hephaestushex/HexMote/assets/Case_(Assembly)_2026-Jul-08_06-05-27PM-000_CustomizedView10271644335_zip/frame.2.png

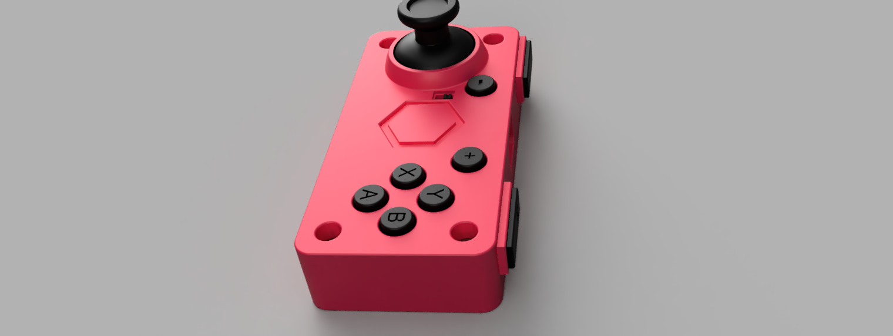
assets/Case_(Assembly)_2026-Jul-08_06-05-27PM-000_CustomizedView10271644335_zip/frame.2.png
